chrisalbertson/Spek1/Hardware/Shoulder/ShoulderBearingHolder.stl

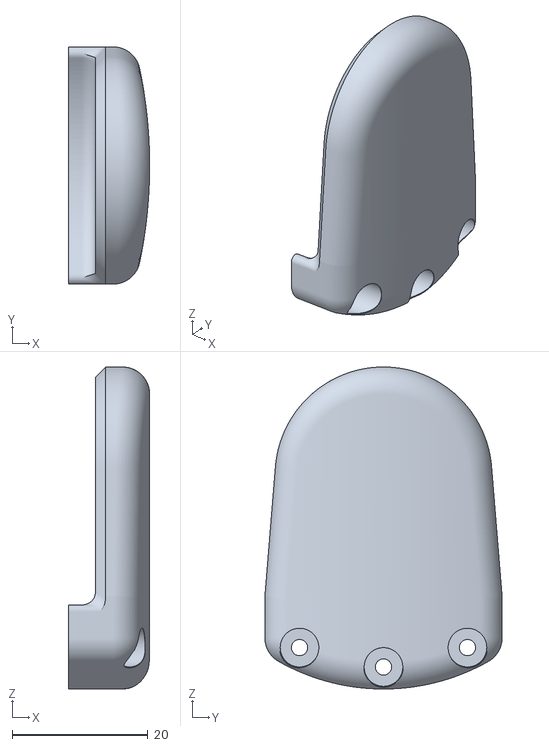
[picture p20: CAD file, 2022-04-30]
Hardware/Shoulder/ShoulderBearingHolder.stl
12.0 x 35.0 x 47.5
