chrisalbertson/Spek1/Hardware/tools/Bearing.stl

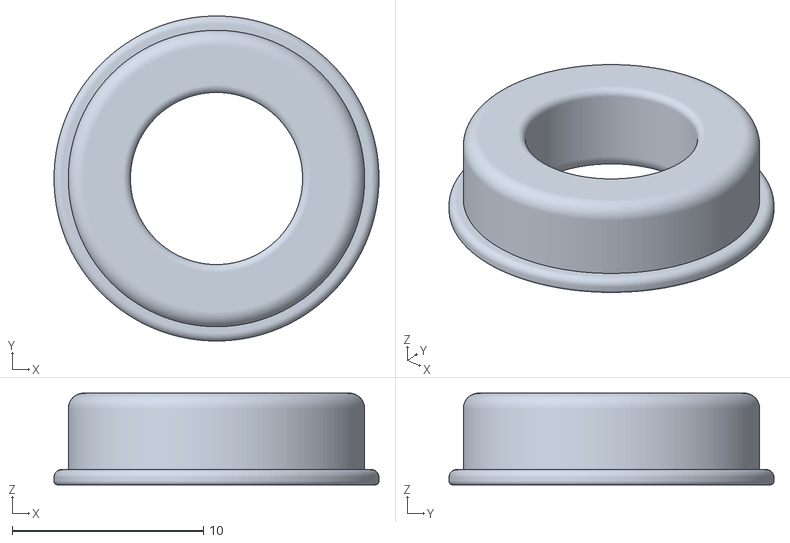
[picture p21: CAD file, 2022-04-30]
Hardware/tools/Bearing.stl
17.0 x 17.0 x 4.80
