chrisalbertson/Spek1/Hardware/Trunk/test_pannel (1).stl

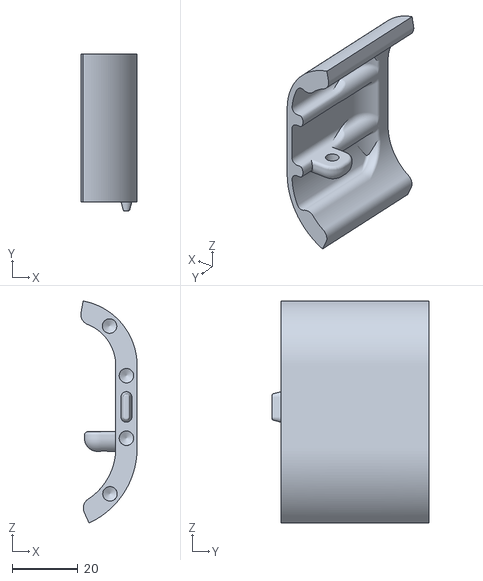
[picture p22: CAD file, 2022-04-30]
Hardware/Trunk/test_pannel (1).stl
17.1 x 47.8 x 67.4
