chrisalbertson/Spek1/Hardware/Legs/foot.stl

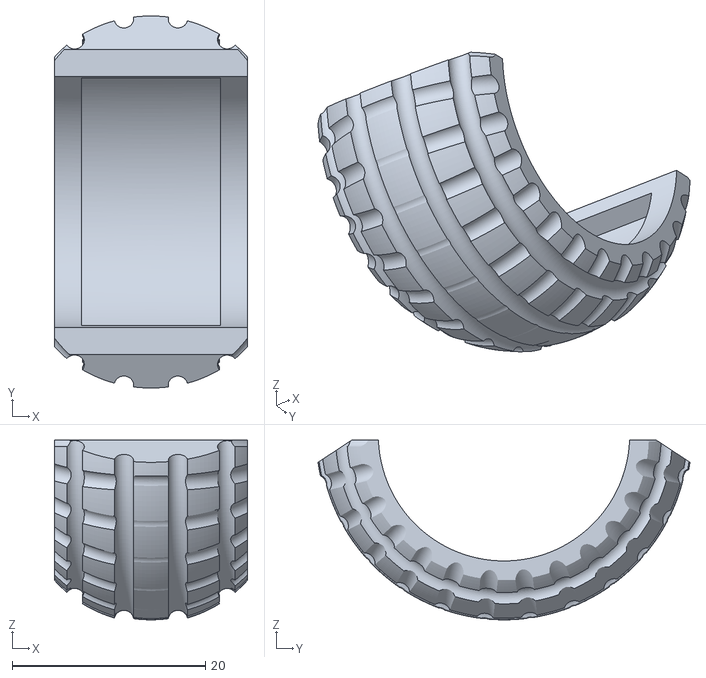
[picture p23: CAD file, 2022-04-30]
Hardware/Legs/foot.stl
20.0 x 38.5 x 18.6
