chrisalbertson/Spek1/Hardware/tools/ServoTop.stl

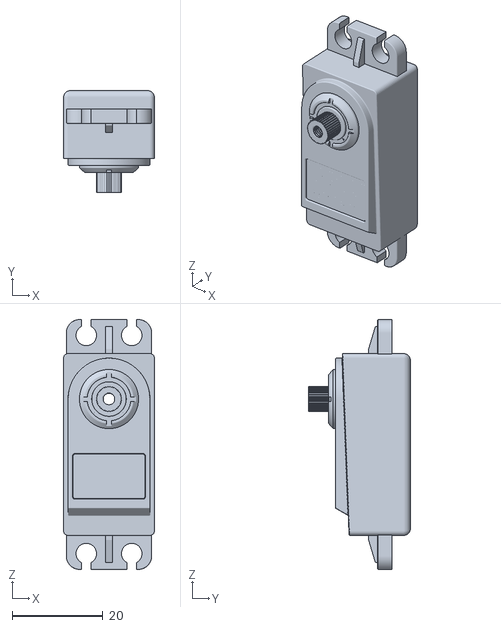
[picture p24: CAD file, 2022-04-30]
Hardware/tools/ServoTop.stl
20.0 x 22.4 x 55.0
