chrisalbertson/Spek1/Hardware/Trunk/side plate.step

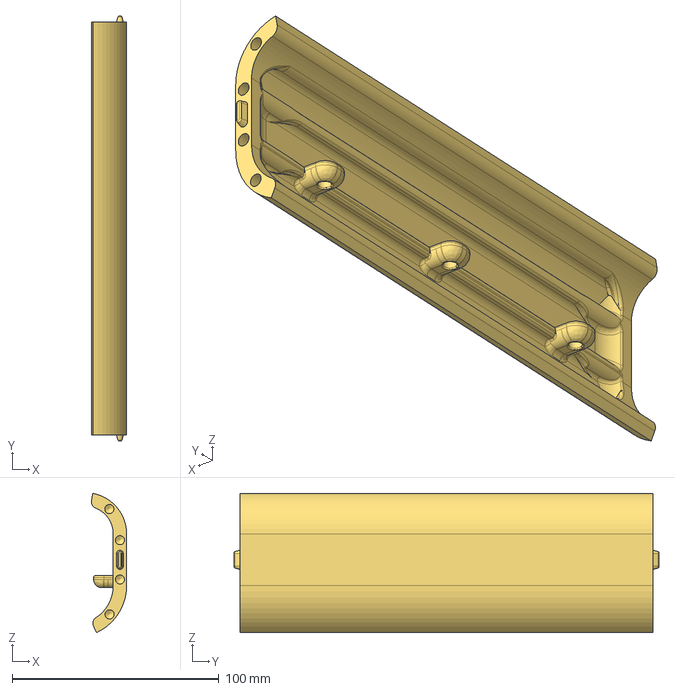
[picture p25: CAD file, 2022-04-30]
Hardware/Trunk/side plate.step
17.1 x 205.6 x 67.4 mm
