chrisalbertson/Spek1/Hardware/covers/cover_tail.stl

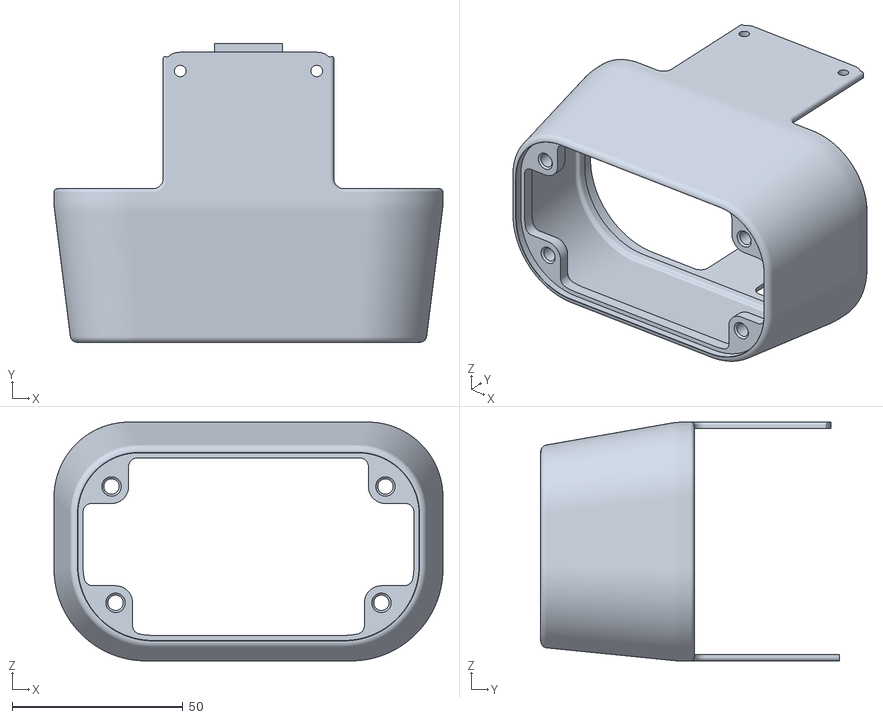
[picture p26: CAD file, 2022-04-30]
Hardware/covers/cover_tail.stl
114.0 x 87.5 x 70.0
