chrisalbertson/Spek1/Hardware/Legs/Left_MidLimb.step

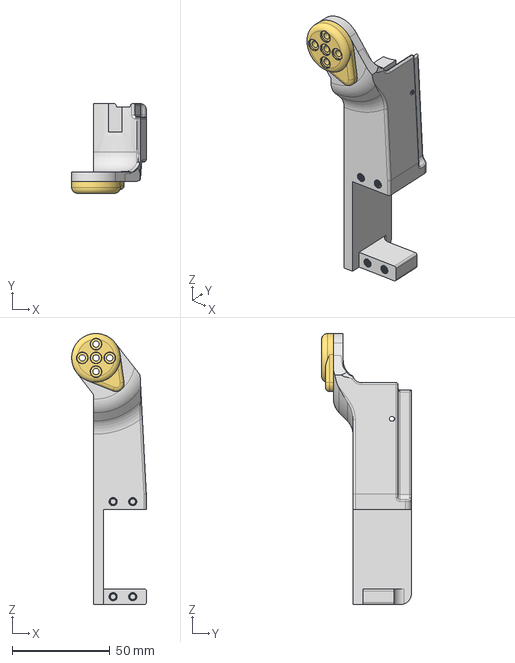
[picture p27: CAD file, 2021-12-10]
Hardware/Legs/Left_MidLimb.step
38.1 x 45.8 x 138.3 mm
F1-B-M3-Heatfit v1 x 5
