chrisalbertson/Spek1/Hardware/Shoulder/AA6_outer_bulkhead.3mf

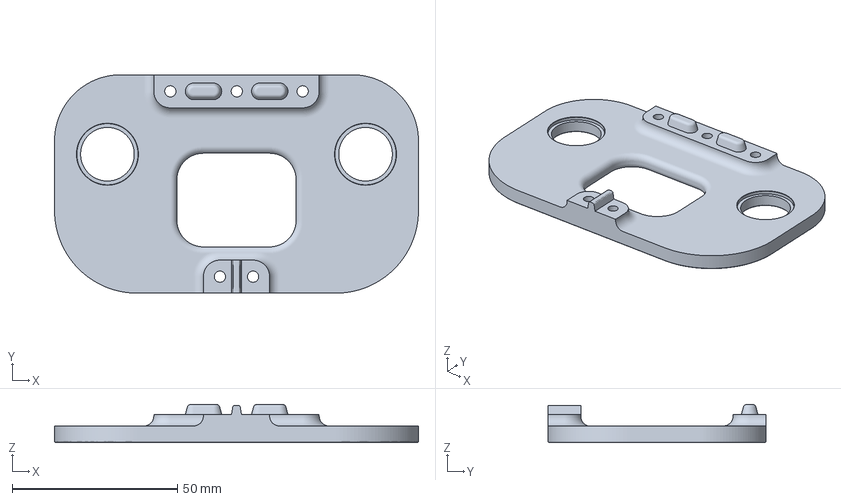
[picture p28: CAD file, 2022-04-30]
Hardware/Shoulder/AA6_outer_bulkhead.3mf
110.0 x 66.0 x 11.5 mm
