chrisalbertson/Spek1/Hardware/Trunk/loop.stl

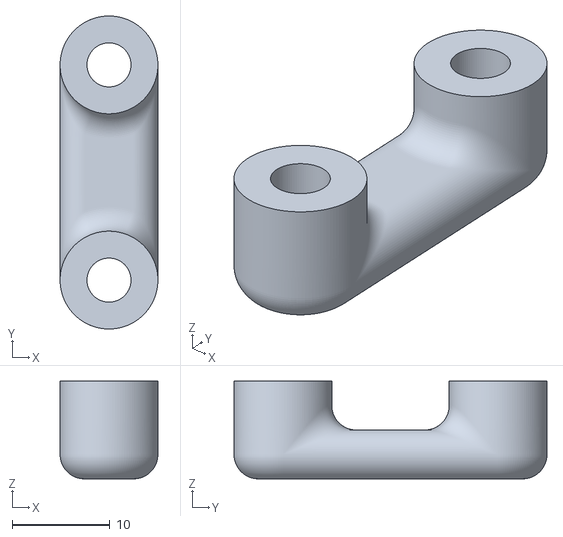
[picture p29: CAD file, 2022-04-30]
Hardware/Trunk/loop.stl
10.0 x 32.0 x 10.0
