chrisalbertson/Spek1/Hardware/covers/Cover_Rear_Plain.stl

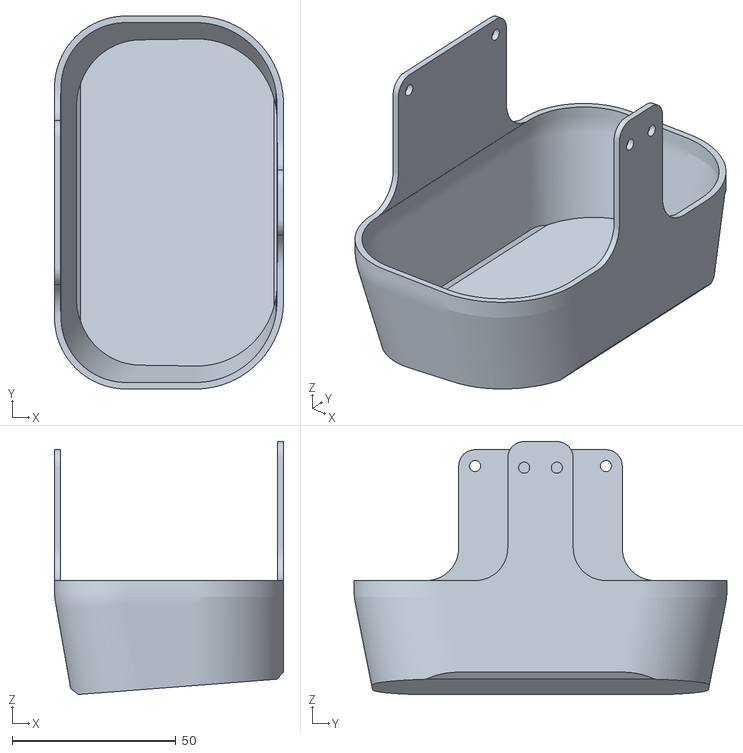
[picture p30: CAD file, 2022-04-30]
Hardware/covers/Cover_Rear_Plain.stl
70.0 x 114.0 x 77.3
