chrisalbertson/Spek1/Hardware/Legs/Left_MidLimb_Cover.step

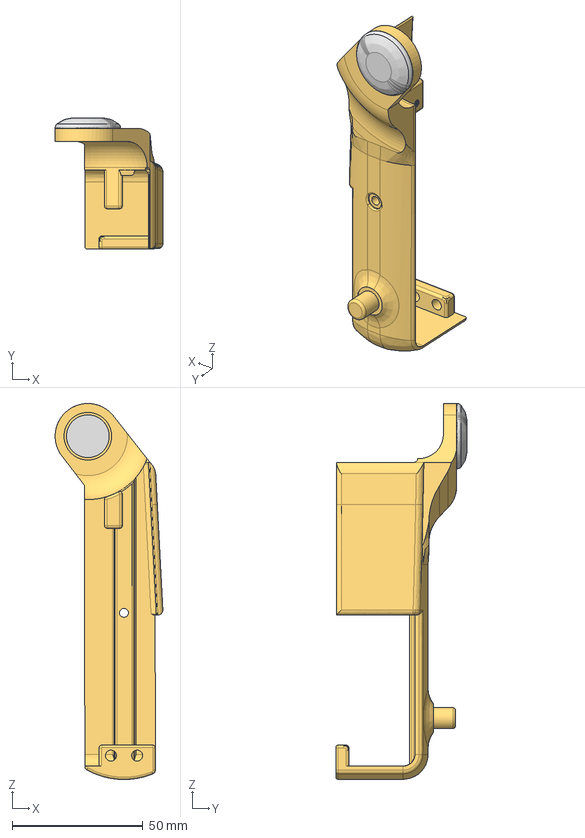
[picture p31: CAD file, 2021-12-10]
Hardware/Legs/Left_MidLimb_Cover.step
41.1 x 50.1 x 143.5 mm
