chrisalbertson/Spek1/Hardware/Shoulder/AA6_side_pannel.3mf

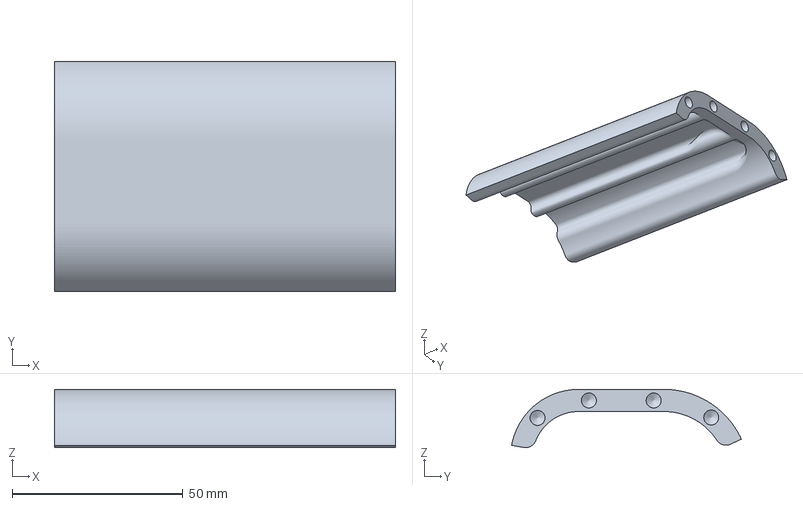
[picture p32: CAD file, 2022-04-30]
Hardware/Shoulder/AA6_side_pannel.3mf
100.0 x 67.4 x 17.1 mm
