chrisalbertson/Spek1/Hardware/tools/AA6_bearings.3mf

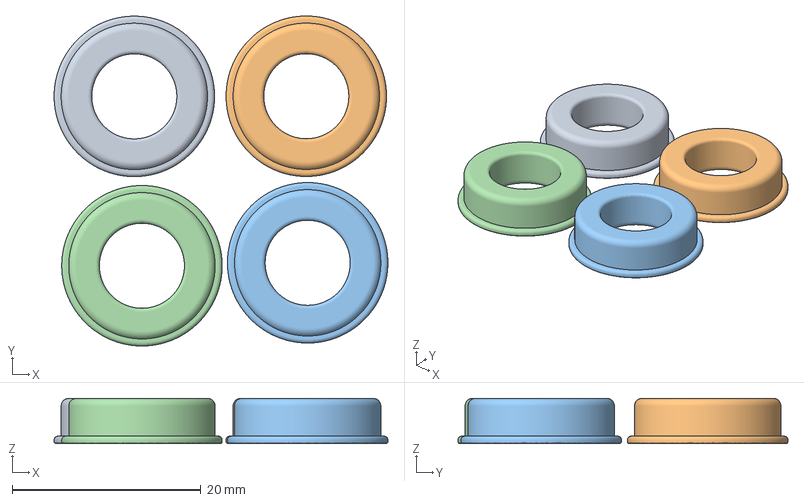
[picture p33: CAD file, 2022-04-30]
Hardware/tools/AA6_bearings.3mf
35.4 x 35.0 x 4.80 mm
Bearing.stl
Bearing.stl(1)
Bearing.stl(2)
Bearing.stl(3)
