chrisalbertson/Spek1/Hardware/Legs/Left_Wrist.step

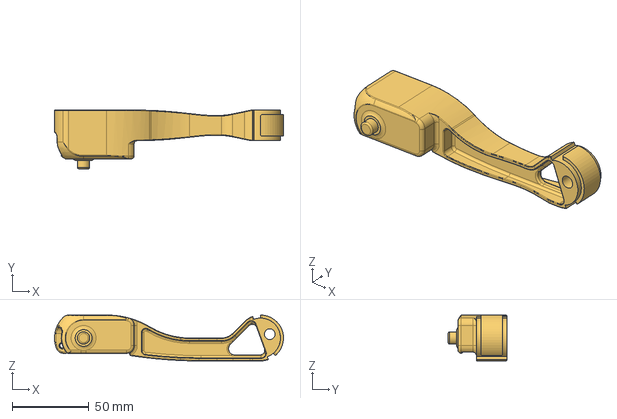
[picture p34: CAD file, 2021-12-09]
Hardware/Legs/Left_Wrist.step
149.6 x 38.4 x 30.0 mm
F1-B-M3-Heatfit v1 (1) x 4
