chrisalbertson/Spek1/Hardware/Legs/upper_leg_mk2/upper leg v13.step

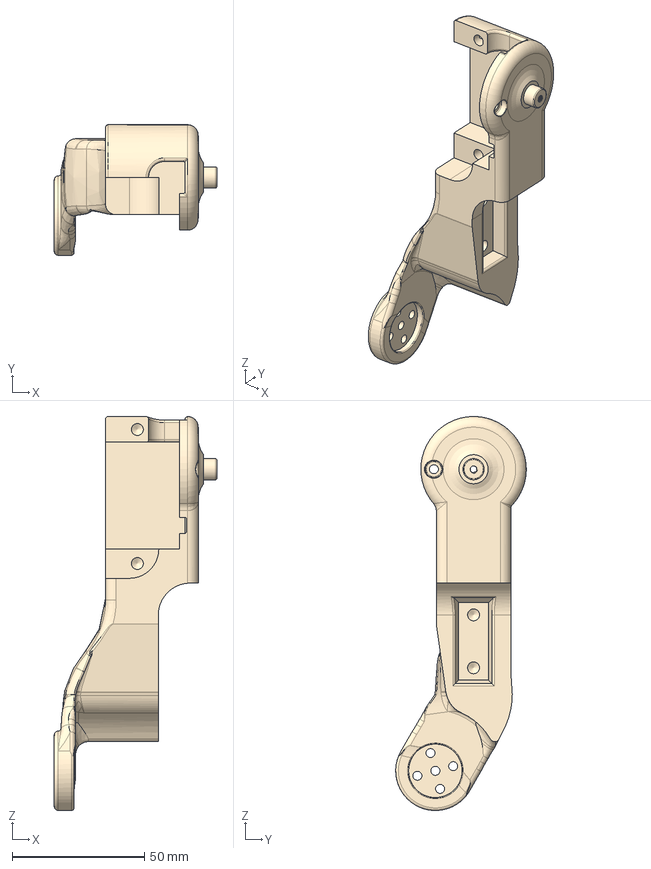
[picture p35: CAD file, 2022-04-30]
Hardware/Legs/upper_leg_mk2/upper leg v13.step
61.4 x 49.3 x 148.8 mm
