chrisalbertson/Spek1/Hardware/Trunk/tray_body_flat.stl

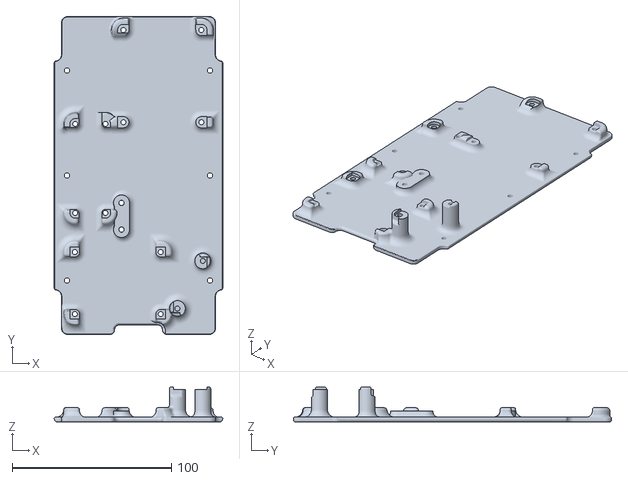
[picture p36: CAD file, 2022-04-30]
Hardware/Trunk/tray_body_flat.stl
106.0 x 200.0 x 22.0
