chrisalbertson/Spek1/Hardware/Legs/upper_leg_mk2/upper_leg_bearing_cover(Mirror).stl

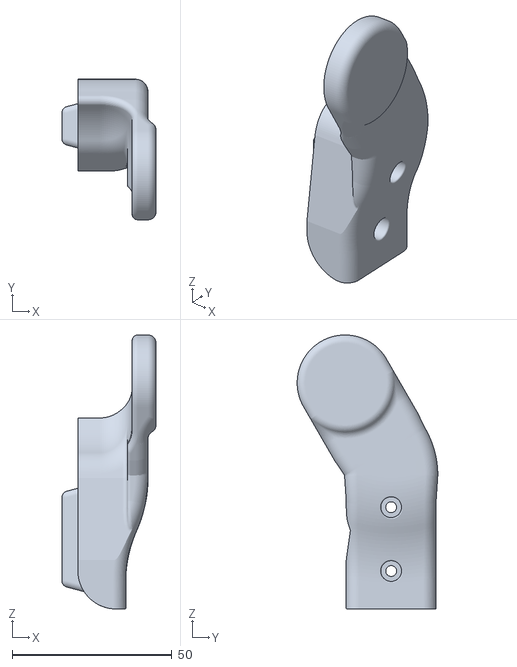
[picture p37: CAD file, 2022-04-30]
Hardware/Legs/upper_leg_mk2/upper_leg_bearing_cover(Mirror).stl
29.5 x 44.1 x 85.9
