chrisalbertson/Spek1/Hardware/Shoulder/AA6_inner_bulkhead.3mf

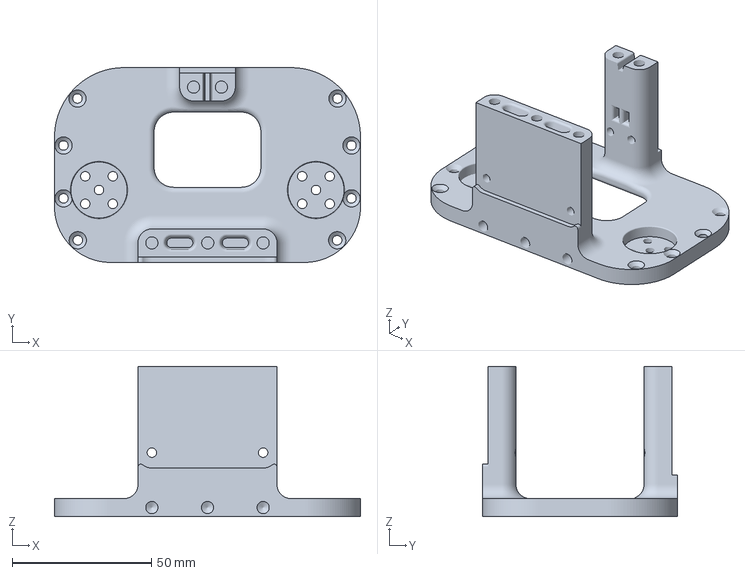
[picture p38: CAD file, 2022-04-30]
Hardware/Shoulder/AA6_inner_bulkhead.3mf
110.0 x 70.0 x 54.0 mm
