chrisalbertson/Spek1/Hardware/Trunk/AA6_tray_Pi4.3mf

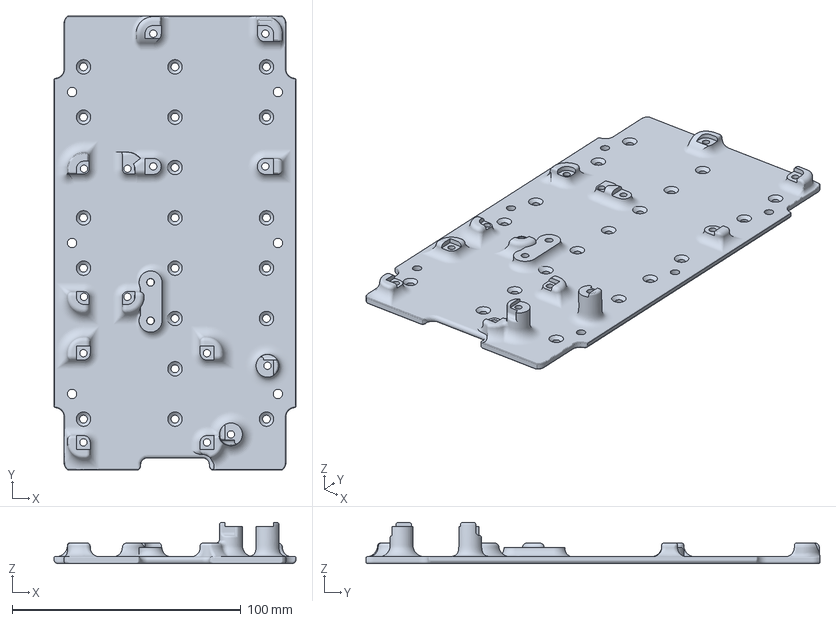
[picture p39: CAD file, 2022-04-30]
Hardware/Trunk/AA6_tray_Pi4.3mf
105.8 x 198.5 x 18.0 mm
