chrisalbertson/Spek1/Hardware/Trunk/tray_flat.stl

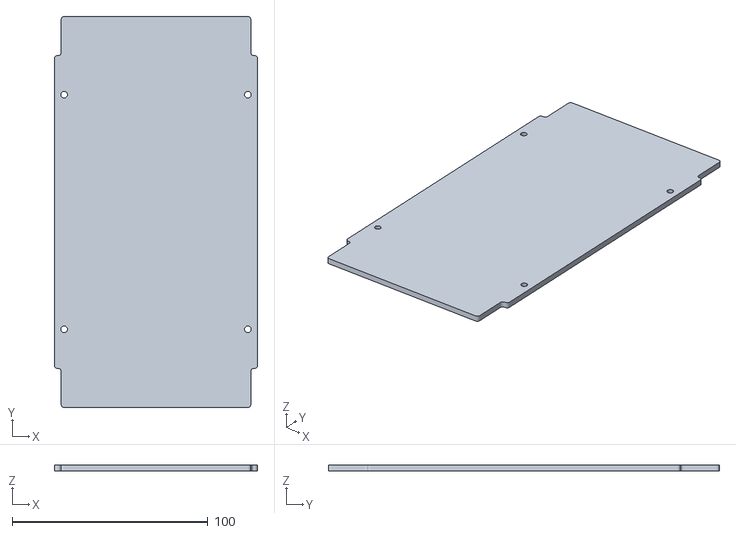
[picture p40: CAD file, 2021-12-07]
Hardware/Trunk/tray_flat.stl
104.0 x 200.0 x 3.00
