chrisalbertson/Spek1/Hardware/Shoulder/AA6_ShoulderBearingCover(Mirror).3mf

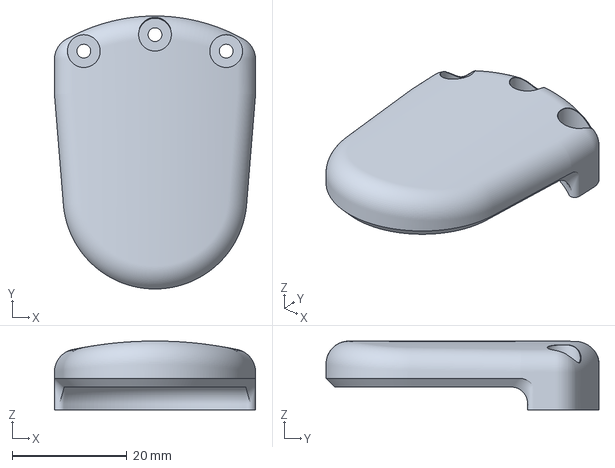
[picture p41: CAD file, 2022-04-30]
Hardware/Shoulder/AA6_ShoulderBearingCover(Mirror).3mf
35.0 x 47.5 x 12.0 mm
