chrisalbertson/Spek1/Hardware/Shoulder/AA6_ShoulderServoCover(Mirror).3mf

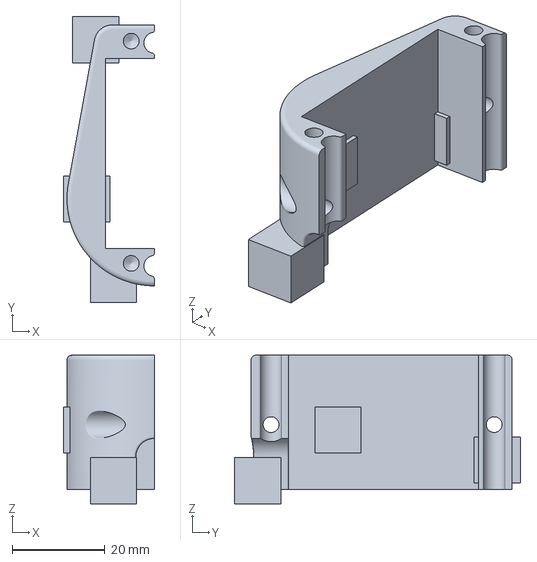
[picture p42: CAD file, 2022-04-30]
Hardware/Shoulder/AA6_ShoulderServoCover(Mirror).3mf
19.6 x 61.8 x 32.1 mm
