chrisalbertson/Spek1/Hardware/Legs/upper_leg_mk2/Print_Tool.stl

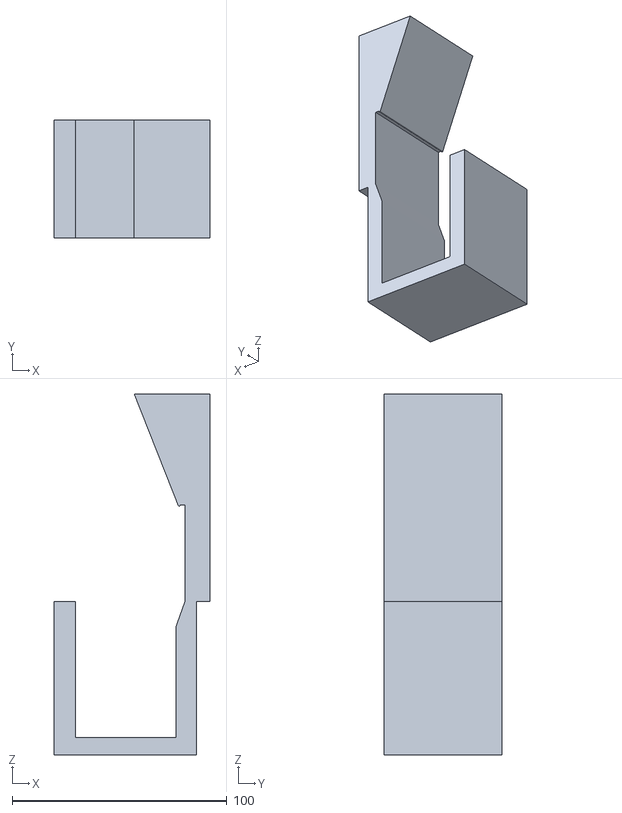
[picture p43: CAD file, 2022-04-30]
Hardware/Legs/upper_leg_mk2/Print_Tool.stl
72.6 x 55.0 x 168.2
