chrisalbertson/Spek1/Software/quad_controller/gui.py

"""
Create the window and runs the event loop for robot GUI.

The Spot controll software is divided into tasks that logically run in parallel.
One task continously runs the motors on the robot to cntrol the position of the
feet and the body.  Exactly what it does, wether it walks, jumps, sits or stands
depends on the values of some global parameters that are shared between all the
tasks.  This module runs a GUI that sets values of these global arameters.

There may be other user interfaces that use an xBox gamepad, voice or a
web browser but they like this user interface just set globals
"""

import logging
import math
log = logging.getLogger(__name__)

import config
if config.ui_web_gui:
    import PySimpleGUIWeb as sg
elif config.ui_x11_gui:
    import PySimpleGUI as sg

import yappi
import robot


def run_gui(robot) -> None:
    """Create the window and run the event loop."""

    walk_speed = 0.0
    crab_speed = 0.0
    walk_turnrate = 0.0
    stance_adjust = 0.0
    body_height_default = 200.0
    body_height = body_height_default
    body_right = 0.0
    body_forward = 0.0
    body_pitch = 0.0
    body_roll = 0.0
    body_yaw = 0.0

    max_sog = 0.1

    if config.ui_x11_gui:
        indent = ((20,0),(0,0)) # padding on left side only
    
        drive_elements = \
            [   [sg.Text('Speed (m/s)', size=(25,1), pad=indent),
                 sg.Text(str(walk_speed), key='-SPEED_TEXT-'),
                 sg.Slider(range = (-max_sog, max_sog),
                           default_value=walk_speed,
                           resolution=max_sog / 20.0,
                           enable_events=True,
                           orientation='h',
                           key='-SPEED-')],

                [sg.Text('Crab (m/s)', size=(25,1), pad=indent),
                 sg.Text(str(crab_speed), key='-CRAB_TEXT-'),
                 sg.Slider(range = (-max_sog, max_sog),
                           default_value=crab_speed,
                           resolution=max_sog / 20.0,
                           enable_events=True,
                           orientation='h',
                           key='-CRAB-')],

                [sg.Text('Z rotaion (rad/s)', size=(25,1), pad=indent),
                 sg.Text(str(walk_turnrate), key='-TURN_TEXT-'),
                 sg.Slider(range = (-3.1, 3.1),
                           default_value=walk_turnrate,
                           resolution=0.1,
                           enable_events=True,
                           orientation='h',
                           key='-TURN-')],

                [sg.Text('Stance Width', size=(25,1), pad=indent),
                 sg.Text(str(stance_adjust), key='-STANCE_ADJUST_TEXT-'),
                 sg.Slider(range = (-25.0, 25.0),
                           default_value=stance_adjust,
                           resolution=1.0,
                           enable_events=True,
                           orientation='h',
                           key='-STANCE_ADJUST-')],


                [sg.Button('WALK',  size=10, key='-WALK-'),
                 sg.Button('STOP',  size=10, key='-STOP-'),
                 sg.Button('STAND', size=10, key='-STAND-')]
            ]
    
        translation_elements = \
            [   [sg.Text('Height', size=(25,1), pad=indent),
                 sg.Text(str(body_height), key='-HEIGHT_TEXT-'),
                 sg.Slider(range = (120.0, 240.0),
                           default_value=body_height_default,
                           resolution=1.0,
                           enable_events=True,
                           orientation='h',
                           key='-HEIGHT-')],

                [sg.Text('Right/Left', size=(25,1), pad=indent),
                 sg.Text(str(body_right), key='-RIGHT_TEXT-'),
                 sg.Slider(range = (-80.0, 80.0),
                           default_value=body_right,
                           resolution=1.0,
                           enable_events=True,
                           orientation='h',
                           key='-RIGHT-')],


                [sg.Text('Fore/Aft', size=(25,1), pad=indent),
                 sg.Text(str(body_forward), key='-FORWARD_TEXT-'),
                 sg.Slider(range = (-80.0, 80.0),
                           default_value=body_forward,
                           resolution=1.0,
                           enable_events=True,
                           orientation='h',
                           key='-FORWARD-')],
                           
               [sg.Button('Reset Translations', size=20, key='-RESET_TRANSLATIONS-')]
            ]
    
        
        rotation_elements = \
            [   [sg.Text('Roll', size=(25,1), pad=indent),
                 sg.Text(str(body_roll), key='-ROLL_TEXT-'),
                 sg.Slider(range = (-20.0, 20.0),
                           default_value=body_roll,
                           resolution=1.0,
                           enable_events=True,
                           orientation='h',
                           key='-ROLL-')],


                [sg.Text('Pitch', size=(25,1), pad=indent),
                 sg.Text(str(body_pitch), key='-PITCH_TEXT-'),
                 sg.Slider(range = (-20.0, 20.0),
                           default_value=body_pitch,
                           resolution=1.0,
                           enable_events=True,
                           orientation='h',
                           key='-PITCH-')],


                [sg.Text('yaw', size=(25,1), pad=indent),
                 sg.Text(str(body_yaw), key='-YAW_TEXT-'),
                 sg.Slider(range = (-20.0, 20.0),
                           default_value=body_yaw,
                           resolution=1.0,
                           enable_events=True,
                           orientation='h',
                           key='-YAW-')],
                           
               [sg.Button('Reset Rotations', size=20, key='-RESET_ROTATIONS-')]
            ]

    
        layout = \
            [      
                [sg.Frame('Driving', drive_elements)],
                [sg.Frame('Body Translation', translation_elements)],
                [sg.Frame('Body Rotation',    rotation_elements)],

                [sg.Button('PANIC', size=10, key='-PANIC-')]
             ]
             
    elif config.ui_web_gui:
        layout_web = [[sg.Text('Speed (m/s)'),
               sg.Text(str(walk_speed), key='-SPEED_TEXT-'),
               sg.Slider(range=(0.0, config.max_forward_speed),
                         default_value=walk_speed,
                         resolution=config.max_forward_speed / 20.0,
                         enable_events=True,
                         orientation='h',
                         key='-SPEED-')],

              [sg.Text('Steering'),
               sg.Text(str(walk_turnrate), key='-TURN_TEXT-'),
               sg.Slider(range=(-1.0, 1.0),
                         default_value=walk_turnrate,
                         resolution=0.01,
                         enable_events=True,
                         orientation='h',
                         key='-TURN-')],

              [sg.Button('WALK', key='-WALK-'),
               sg.Button('STOP', key='-STOP-'),
               sg.Button('PANIC', key='-PANIC-')]
              ]

    if config.ui_web_gui:
        window = sg.Window('Walk Web GUI', layout_web, web_port=2222, web_start_browser=False)
    elif config.ui_x11_gui:
        window = sg.Window('Walk GUI', layout)

    while True:  # Event Loop
        event, values = window.read()

        if event in (None, 'Exit'):
            break

        elif event == '-SPEED-':
            walk_speed = float(values['-SPEED-'])
            window['-SPEED_TEXT-'].update(str(walk_speed))
            robot.set_velocity(walk_speed, crab_speed, walk_turnrate)

        elif event == '-CRAB-':
            crab_speed = float(values['-CRAB-'])
            window['-CRAB_TEXT-'].update(str(crab_speed))
            robot.set_velocity(walk_speed, crab_speed, walk_turnrate)

        elif event == '-TURN-':
            walk_turnrate = values['-TURN-']
            window['-TURN_TEXT-'].update(str(walk_turnrate))
            robot.set_velocity(walk_speed, crab_speed, walk_turnrate)

        elif event == '-STANCE_ADJUST-':
            stance_adjust = values['-STANCE_ADJUST-']
            window['-STANCE_ADJUST_TEXT-'].update(str(stance_adjust))
            robot.set_stance_width(stance_adjust/1000.0)  # convert mm to meters

        elif event == '-HEIGHT-':
            body_height = values['-HEIGHT-']
            window['-HEIGHT_TEXT-'].update(str(body_height))
            robot.set_body_center((body_forward/1000.0, body_right/1000.0, body_height/1000.0))

        elif event == '-RIGHT-':
            body_right = values['-RIGHT-']
            window['-RIGHT_TEXT-'].update(str(body_right))
            robot.set_body_center((body_forward/1000.0, body_right/1000.0, body_height/1000.0))

        elif event == '-FORWARD-':
            body_forward = values['-FORWARD-']
            window['-FORWARD_TEXT-'].update(str(body_forward))
            robot.set_body_center((body_forward/1000.0, body_right/1000.0, body_height/1000.0))
            
        
            
        elif event == '-RESET_TRANSLATIONS-':
            body_height  = body_height_default
            body_right   = 0.0
            body_forward = 0.0
            window['-HEIGHT_TEXT-'].update(str(body_height))
            window['-RIGHT_TEXT-'].update(str(body_right))
            window['-FORWARD_TEXT-'].update(str(body_forward))
            window['-HEIGHT-'].update(body_height)
            window['-RIGHT-'].update(body_right)
            window['-FORWARD-'].update(body_forward)
            robot.set_body_center((body_forward/1000.0, body_right/1000.0, body_height/1000.0))

        elif event == '-ROLL-':
            body_roll = values['-ROLL-']
            window['-ROLL_TEXT-'].update(str(body_roll))
            robot.set_body_angles((math.radians(body_roll), math.radians(body_pitch), math.radians(body_yaw)))

        elif event == '-PITCH-':
            body_pitch = values['-PITCH-']
            window['-PITCH_TEXT-'].update(str(body_pitch))
            robot.set_body_angles((math.radians(body_roll), math.radians(body_pitch), math.radians(body_yaw)))

        elif event == '-YAW-':
            body_yaw = values['-YAW-']
            window['-YAW_TEXT-'].update(str(body_yaw))
            robot.set_body_angles((math.radians(body_roll), math.radians(body_pitch), math.radians(body_yaw)))
            
        elif event == '-RESET_ROTATIONS-':
            body_roll  = 0.0
            body_pitch = 0.0
            body_yaw   = 0.0
            window['-ROLL_TEXT-'].update(str(body_roll))
            window['-PITCH_TEXT-'].update(str(body_pitch))
            window['-YAW_TEXT-'].update(str(body_yaw))
            window['-ROLL-'].update(body_roll)
            window['-PITCH-'].update(body_pitch)
            window['-YAW-'].update(body_yaw)
            robot.set_body_angles((math.radians(body_roll), math.radians(body_pitch), math.radians(body_yaw)))
            
        elif event == '-WALK-':
            robot.walk(walk_speed, crab_speed, walk_turnrate)

        elif event == '-STAND-':
            robot.stand(1.0)

        elif event == '-STOP-':
            walk_speed    = 0.0
            crab_speed    = 0.0
            walk_turnrate = 0.0
            robot.set_velocity(walk_speed, crab_speed, walk_turnrate)

            window['-SPEED-'].update(str(walk_speed))
            window['-SPEED_TEXT-'].update(str(walk_speed))
            window['-CRAB-'].update(str(walk_speed))
            window['-CRAB_TEXT-'].update(str(walk_speed))
            window['-TURN-'].update(str(walk_turnrate))
            window['-TURN_TEXT-'].update(str(walk_turnrate))

        elif event == '-PANIC-':
            break

    robot.kill()
    window.close()
    return


if __name__ == "__main__":
    logging.basicConfig(filename='quad_controller.log',
                        filemode='w',
                        level=logging.WARNING, )

    config.UsePCA9685Hardware = True

    yappi.start()

    log.info('Starting GUI')
    run_gui()
    log.info('normal termination')

    yappi.get_func_stats().print_all()
    yappi.get_thread_stats().print_all()
