chrisalbertson/Spek1/Software/testing/mpu6050_demo.py

import time
import board
import adafruit_mpu6050

i2c = board.I2C()  # uses board.SCL and board.SDA
mpu = adafruit_mpu6050.MPU6050(i2c)

# set some properties
mpu.accelerometer_range = adafruit_mpu6050.Range.RANGE_2_G
mpu.filter_bandwidth    = adafruit_mpu6050.Bandwidth.BAND_10_HZ
mpu.gyro_range          = adafruit_mpu6050.GyroRange.RANGE_250_DPS

while True:
    print("Acceleration: X:%.2f, Y: %.2f, Z: %.2f m/s^2" % (mpu.acceleration))
    print("Gyro X:%.2f, Y: %.2f, Z: %.2f rad/s" % (mpu.gyro))
    print("Temperature: %.2f C" % mpu.temperature)
    print("")
    time.sleep(1)
